ozarchie/EQMOD-WiFi/Documentation/images/EQMODWiFi_schem.png

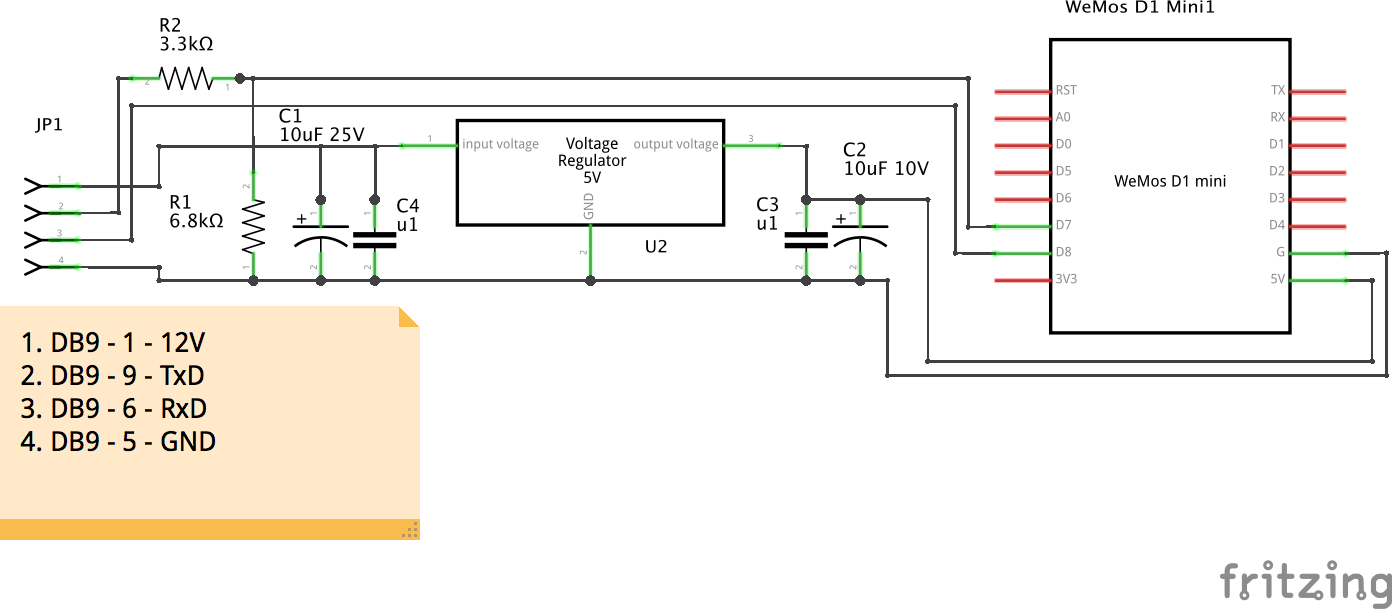
Documentation/images/EQMODWiFi_schem.png
