ozarchie/EQMOD-WiFi/Documentation/images/EQMODWiFiAndroid-1.png

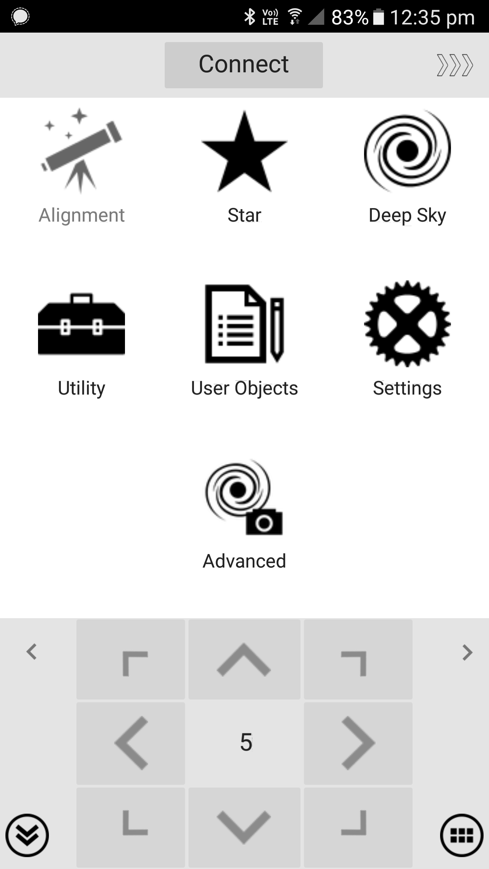
Documentation/images/EQMODWiFiAndroid-1.png
