ozarchie/EQMOD-WiFi/Documentation/images/EQMODWiFiAndroid-2.png

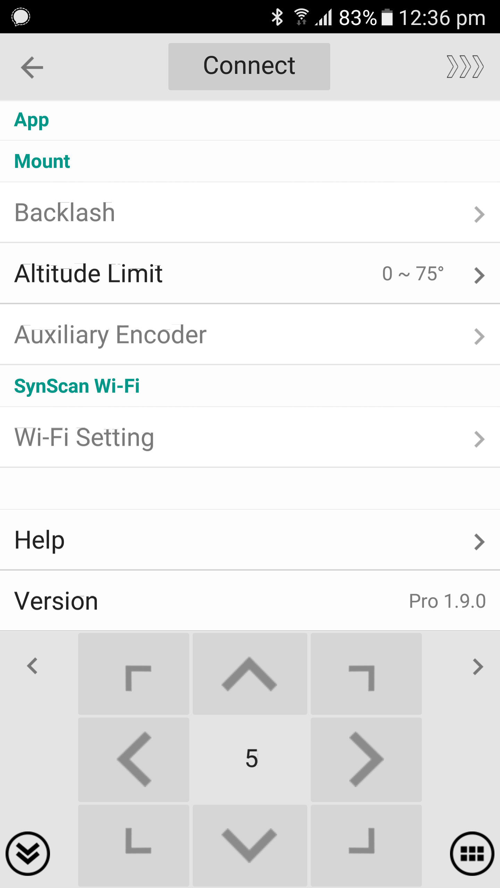
Documentation/images/EQMODWiFiAndroid-2.png
