ozarchie/EQMOD-WiFi/Documentation/images/EQMODWiFiAndroid-3.png

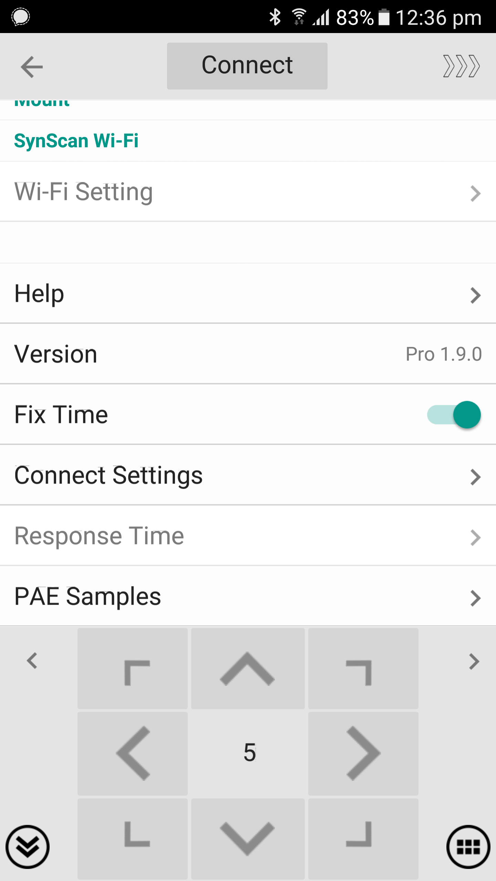
Documentation/images/EQMODWiFiAndroid-3.png
