ozarchie/EQMOD-WiFi/Documentation/images/EQMODWiFiAndroid-5.png

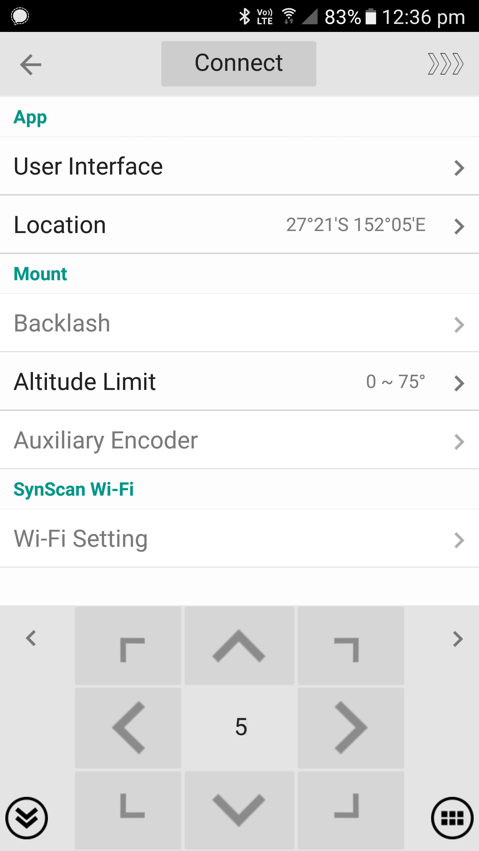
Documentation/images/EQMODWiFiAndroid-5.png
