ozarchie/EQMOD-WiFi/Documentation/images/EQMODWiFiAndroid-6.png

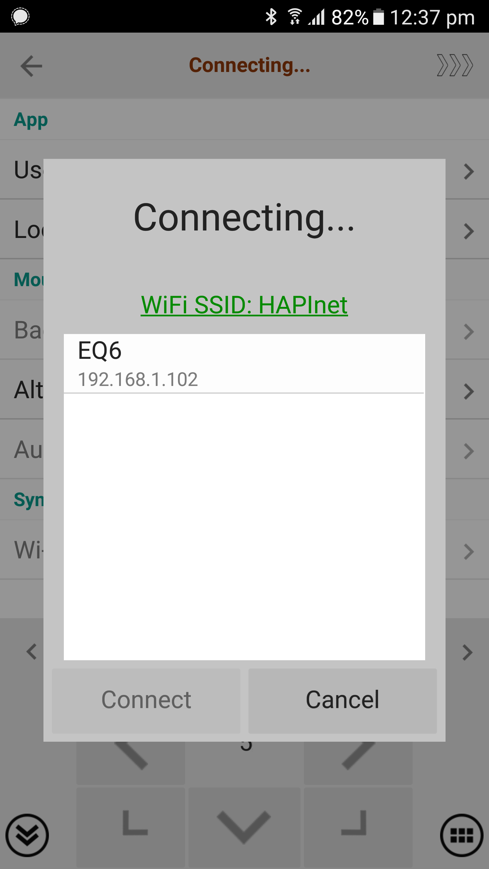
Documentation/images/EQMODWiFiAndroid-6.png
