ozarchie/EQMOD-WiFi/Documentation/images/EQMODWiFiAndroid-7.png

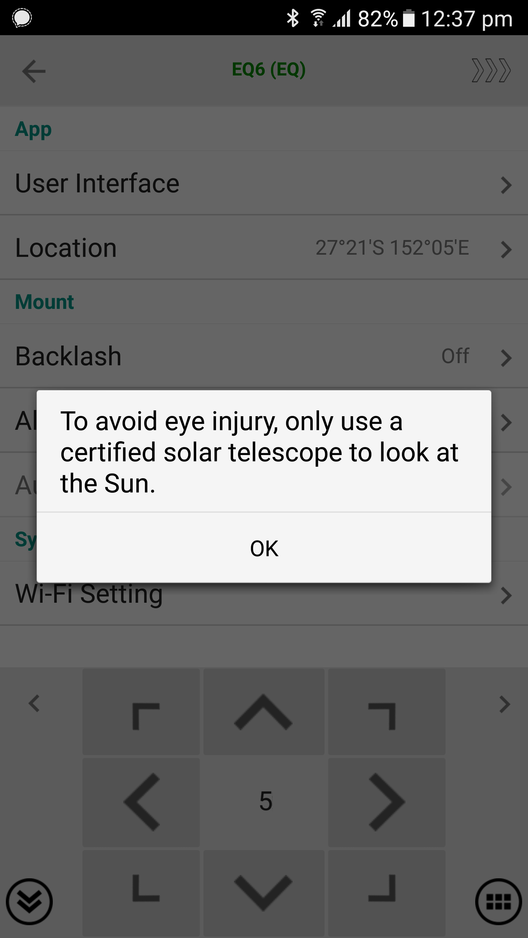
Documentation/images/EQMODWiFiAndroid-7.png
