ozarchie/EQMOD-WiFi/Documentation/images/EQMODWiFiWin-5.PNG

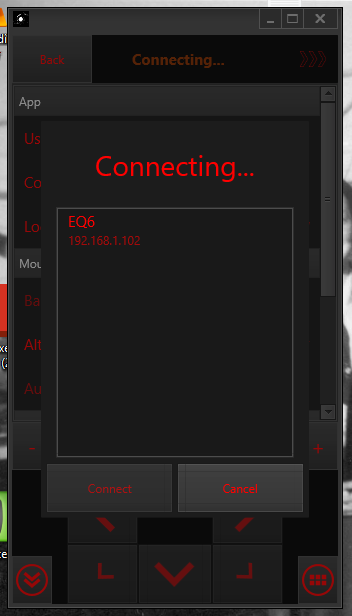
Documentation/images/EQMODWiFiWin-5.PNG
