ozarchie/EQMOD-WiFi/Documentation/images/EQMODWiFiWin-6.PNG

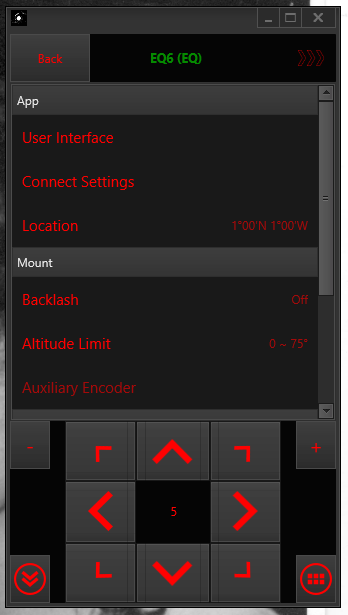
Documentation/images/EQMODWiFiWin-6.PNG
