ozarchie/EQMOD-WiFi/Software/DualDevice/ESP28266SerialServer/myesp_now.h

// Copyright 2015-2016 Espressif Systems (Shanghai) PTE LTD
//
// Licensed under the Apache License, Version 2.0 (the "License");
// you may not use this file except in compliance with the License.
// You may obtain a copy of the License at

//     http://www.apache.org/licenses/LICENSE-2.0
//
// Unless required by applicable law or agreed to in writing, software
// distributed under the License is distributed on an "AS IS" BASIS,
// WITHOUT WARRANTIES OR CONDITIONS OF ANY KIND, either express or implied.
// See the License for the specific language governing permissions and
// limitations under the License.

#ifndef __ESP_NOW_H__
#define __ESP_NOW_H__

#ifdef __cplusplus
extern "C" {
#endif
typedef int32_t esp_err_t;

/* Definitions for error constants. */
#define ESP_OK          0       /*!< esp_err_t value indicating success (no error) */
#define ESP_FAIL        -1      /*!< Generic esp_err_t code indicating failure */

#define ESP_ERR_NO_MEM          0x101   /*!< Out of memory */
#define ESP_ERR_INVALID_ARG     0x102   /*!< Invalid argument */
#define ESP_ERR_INVALID_STATE   0x103   /*!< Invalid state */
#define ESP_ERR_INVALID_SIZE    0x104   /*!< Invalid size */
#define ESP_ERR_NOT_FOUND       0x105   /*!< Requested resource not found */
#define ESP_ERR_NOT_SUPPORTED   0x106   /*!< Operation or feature not supported */
#define ESP_ERR_TIMEOUT         0x107   /*!< Operation timed out */
#define ESP_ERR_INVALID_RESPONSE    0x108   /*!< Received response was invalid */
#define ESP_ERR_INVALID_CRC     0x109   /*!< CRC or checksum was invalid */
#define ESP_ERR_INVALID_VERSION     0x10A   /*!< Version was invalid */
#define ESP_ERR_INVALID_MAC     0x10B   /*!< MAC address was invalid */

#define ESP_ERR_WIFI_BASE       0x3000 /*!< Starting number of WiFi error codes */
#define ESP_ERR_MESH_BASE       0x4000 /*!< Starting number of MESH error codes */

/**
  * @brief Returns string for esp_err_t error codes
  *
  * This function finds the error code in a pre-generated lookup-table and
  * returns its string representation.
  *
  * The function is generated by the Python script
  * tools/gen_esp_err_to_name.py which should be run each time an esp_err_t
  * error is modified, created or removed from the IDF project.
  *
  * @param code esp_err_t error code
  * @return string error message
  */
const char *esp_err_to_name(esp_err_t code);

/**
  * @brief Returns string for esp_err_t and system error codes
  *
  * This function finds the error code in a pre-generated lookup-table of
  * esp_err_t errors and returns its string representation. If the error code
  * is not found then it is attempted to be found among system errors.
  *
  * The function is generated by the Python script
  * tools/gen_esp_err_to_name.py which should be run each time an esp_err_t
  * error is modified, created or removed from the IDF project.
  *
  * @param code esp_err_t error code
  * @param[out] buf buffer where the error message should be written
  * @param buflen Size of buffer buf. At most buflen bytes are written into the buf buffer (including the terminating null byte).
  * @return buf containing the string error message
  */
const char *esp_err_to_name_r(esp_err_t code, char *buf, size_t buflen);

/** @cond */
void _esp_error_check_failed(esp_err_t rc, const char *file, int line, const char *function, const char *expression) __attribute__((noreturn));

/** \defgroup WiFi_APIs WiFi Related APIs
  * @brief WiFi APIs
  */

/** @addtogroup WiFi_APIs
  * @{
  */

/** \defgroup ESPNOW_APIs  ESPNOW APIs
  * @brief ESP32 ESPNOW APIs
  *
  */

/** @addtogroup ESPNOW_APIs
  * @{
  */

#define ESP_ERR_ESPNOW_BASE         (ESP_ERR_WIFI_BASE + 100) /*!< ESPNOW error number base. */
#define ESP_ERR_ESPNOW_NOT_INIT     (ESP_ERR_ESPNOW_BASE + 1) /*!< ESPNOW is not initialized. */
#define ESP_ERR_ESPNOW_ARG          (ESP_ERR_ESPNOW_BASE + 2) /*!< Invalid argument */
#define ESP_ERR_ESPNOW_NO_MEM       (ESP_ERR_ESPNOW_BASE + 3) /*!< Out of memory */
#define ESP_ERR_ESPNOW_FULL         (ESP_ERR_ESPNOW_BASE + 4) /*!< ESPNOW peer list is full */
#define ESP_ERR_ESPNOW_NOT_FOUND    (ESP_ERR_ESPNOW_BASE + 5) /*!< ESPNOW peer is not found */
#define ESP_ERR_ESPNOW_INTERNAL     (ESP_ERR_ESPNOW_BASE + 6) /*!< Internal error */
#define ESP_ERR_ESPNOW_EXIST        (ESP_ERR_ESPNOW_BASE + 7) /*!< ESPNOW peer has existed */
#define ESP_ERR_ESPNOW_IF           (ESP_ERR_ESPNOW_BASE + 8) /*!< Interface error */

#define ESP_NOW_ETH_ALEN             6         /*!< Length of ESPNOW peer MAC address */
#define ESP_NOW_KEY_LEN              16        /*!< Length of ESPNOW peer local master key */

#define ESP_NOW_MAX_TOTAL_PEER_NUM   20        /*!< Maximum number of ESPNOW total peers */
#define ESP_NOW_MAX_ENCRYPT_PEER_NUM 6         /*!< Maximum number of ESPNOW encrypted peers */

#define ESP_NOW_MAX_DATA_LEN         250       /*!< Maximum length of ESPNOW data which is sent very time */

/**
 * @brief Status of sending ESPNOW data .
 */
typedef enum {
    ESP_NOW_SEND_SUCCESS = 0,       /**< Send ESPNOW data successfully */
    ESP_NOW_SEND_FAIL,              /**< Send ESPNOW data fail */
} esp_now_send_status_t;

#ifdef __cplusplus
}
#endif

#endif /* __ESP_NOW_H__ */
